Tetris2102/Nuclear_Lego/Base_Hardware/3D printing sent on Dec.12/PCBHolder.stl

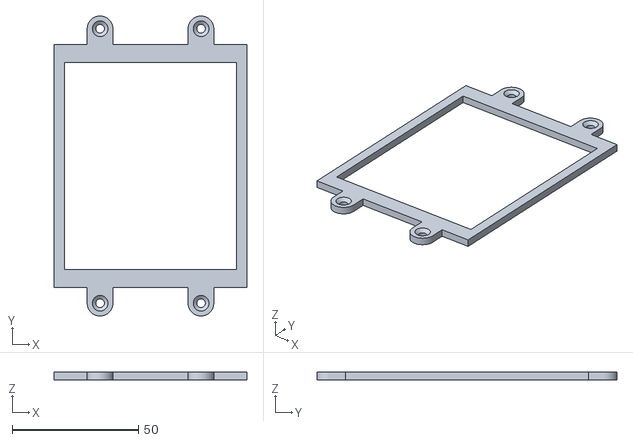
[picture p12: CAD file, 2026-01-09]
Base_Hardware/3D printing sent on Dec.12/PCBHolder.stl
76.5 x 118.9 x 3.00
