Tetris2102/Nuclear_Lego/Base_Hardware/3D printing sent on Dec.12/BaseLid.stl

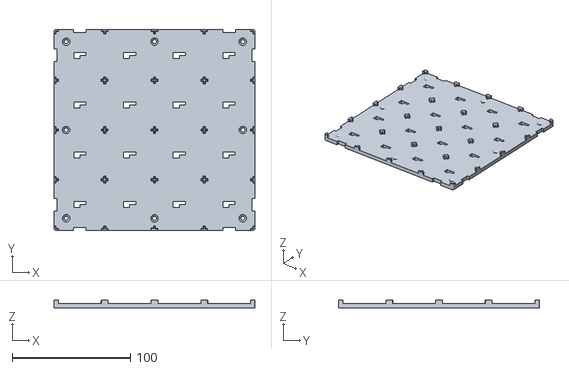
[picture p13: CAD file, 2026-01-09]
Base_Hardware/3D printing sent on Dec.12/BaseLid.stl
170.0 x 170.0 x 7.00
