Tetris2102/Nuclear_Lego/Particle_Transport/include/isotopeSample.h

// isotopeSample.h

#ifndef IsotopeSample_H
#define IsotopeSample_H

#include "vector3.h"
#include "particleGroup.h"
#include <string>
#include <vector>
#include <random>
#include <cstdint>

// Mass of source is considered constant
class IsotopeSample {
    private:
        std::string name;
        float activity;
        ParticleType emissionParticleGroup;
        float emissionEnergy;

        void normalizeV(Vector3 &dirXYZ);
    public:
        // For radioactive samples
        IsotopeSample(std::string _name, ParticleType _emissionParticleGroup,
          float _emissionEnergy, float _activity = 0.0) {
            name = _name;
            activity = _activity;
            emissionParticleGroup = _emissionParticleGroup;
            emissionEnergy = _emissionEnergy;
        }

        // For stable samples
        IsotopeSample() {
            activity = 0.0;
        }

        // IsotopeSample(const IsotopeSample&) = delete;
        // IsotopeSample& operator=(const IsotopeSample&) = delete;
        //
        // IsotopeSample(IsotopeSample&&) noexcept = default;
        // IsotopeSample& operator=(IsotopeSample&&) noexcept = default;

        // Create a particle list with uniform distribution in space
        std::vector<ParticleGroup> generateParticleGroups(
          float timeElapsed, Vector3 originXYZ, uint16_t partGroupSize,
          std::uniform_real_distribution<float>& dist, std::mt19937& gen);
        std::string getName();
        void setActivity(float a);
        float getActivity();
        void setEmitParticleGroupType(ParticleType pt);
        ParticleType getEmitParticleGroupType();
        float getEmitEnergy();
        bool isRadioactive();
};

#endif
