Tetris2102/Nuclear_Lego/Particle_Transport/test_files/worldTestBasic.cpp

#include "world.h"
#include "../Data/data.cpp"
#include <vector>
#include <random>
#include <iostream>

int main(int argc, char const *argv[]) {
    Material airMat = getAir();
    float voxelSide = 2.0;

    std::random_device rd;
    std::mt19937 gen(rd());
    std::uniform_real_distribution<float> dist(0, 1);
    Voxel air(voxelSide, MATTER, Vector3{0.0, 0.0, 0.0}, airMat);
    air.setRNG(dist, gen);

    IsotopeSample alphaSample("alphaSample", ALPHA, 2.1, 2000);
    Voxel sourceInAir(voxelSide, SOURCE, Vector3{0.0, 0.0, 0.0},
      airMat, alphaSample);
    sourceInAir.setRNG(dist, gen);

    const short int x = 3, y = 3, z = 3;

    World world(x, y, z, voxelSide);
    std::vector<Voxel> scene = {
        air, air, air, air,     air,     air, air, air, air,
        air, air, air, air, sourceInAir, air, air, air, air,
        air, air, air, air,     air,     air, air, air, air
    };
    world.setScene(scene);
    for(int i = 0; i<10; i++) {
        world.simulate(0.5);
        std::cout << "Active particles: " << world.getParticleGroupCount()
          << "." << std::endl;
    }
    std::cout << "Emitted: " << sourceInAir.getPartsEmitted(5.0)
      << "." << std::endl;

    return 0;
}
